muke24/Alert-Detector/Source/Images/background1.png

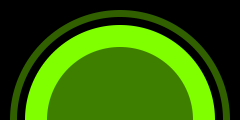
Source/Images/background1.png
