muke24/Alert-Detector/Source/Images/backgroundWhite1.png

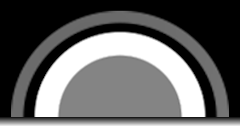
Source/Images/backgroundWhite1.png
