muke24/Alert-Detector/Source/Images/backgroundWhite.png

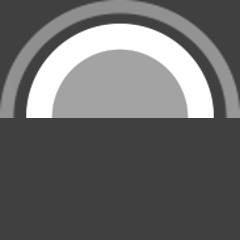
Source/Images/backgroundWhite.png
