muke24/Alert-Detector/Source/Images/In Use/Resources/Compass/compassBackground.png

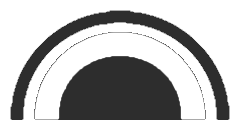
Source/Images/In Use/Resources/Compass/compassBackground.png
