muke24/Alert-Detector/Source/Images/In Use/Resources/Compass/compassBackground_1.png

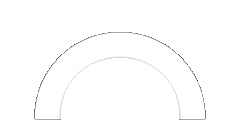
Source/Images/In Use/Resources/Compass/compassBackground_1.png
