muke24/Alert-Detector/Source/Images/In Use/Resources/Heat/heatBar1_full_img.png

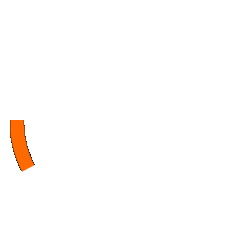
Source/Images/In Use/Resources/Heat/heatBar1_full_img.png
