muke24/Alert-Detector/Source/Images/In Use/Resources/Heat/heatBar2_full_img.png

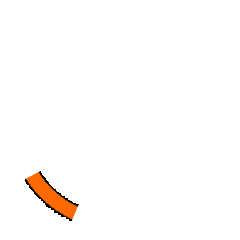
Source/Images/In Use/Resources/Heat/heatBar2_full_img.png
