muke24/Alert-Detector/Source/Images/In Use/Resources/Heat/heatBar3_full_img.png

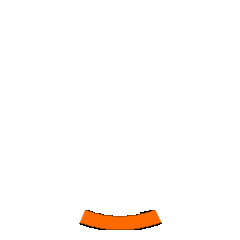
Source/Images/In Use/Resources/Heat/heatBar3_full_img.png
