muke24/Alert-Detector/Models/15/Print/Separate/ModuleHolder.stl

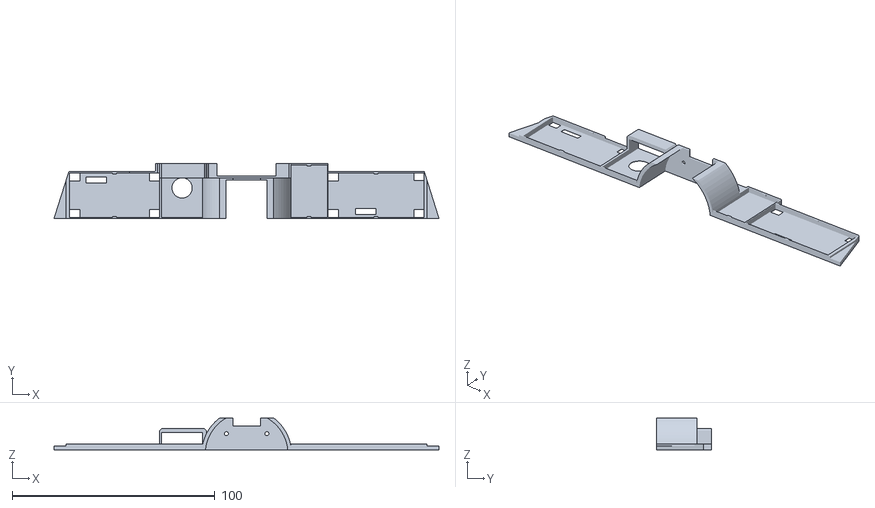
[picture p28: CAD file, 2025-08-17]
Models/15/Print/Separate/ModuleHolder.stl
189.9 x 27.0 x 15.7
