muke24/Alert-Detector/Models/New Small/Enclosure/01/Print/PoliceRadar03_Flipped.stl

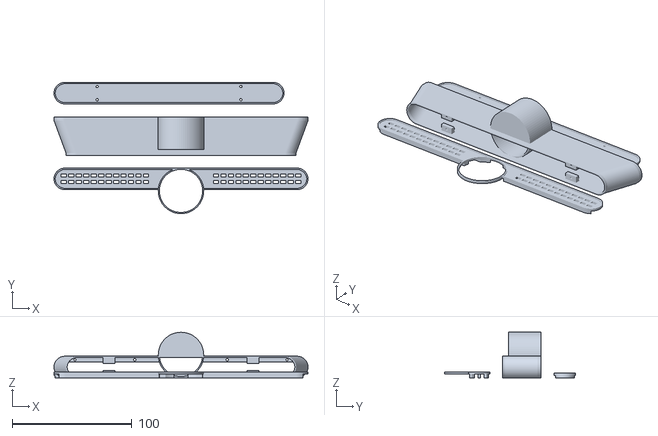
[picture p29: CAD file, 2025-07-22]
Models/New Small/Enclosure/01/Print/PoliceRadar03_Flipped.stl
212.0 x 109.6 x 38.0
