muke24/Alert-Detector/Models/New Small/Enclosure/01/Print/Separate/05/PoliceRadar05_Lid.stl

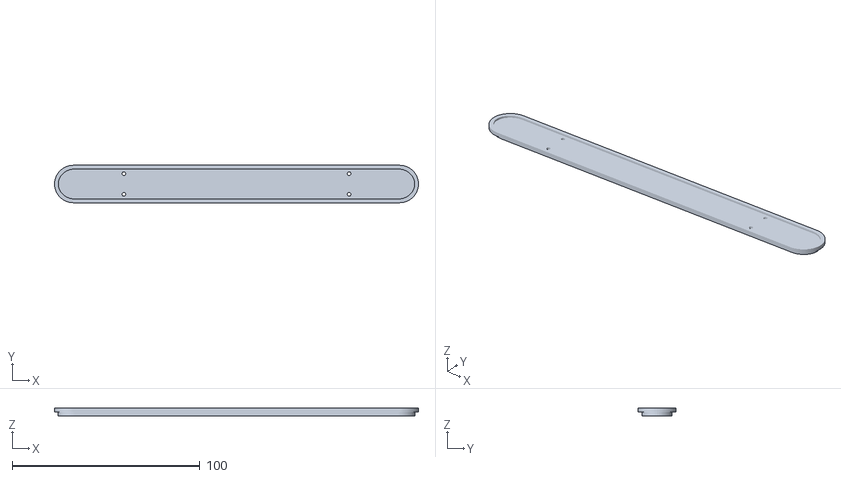
[picture p30: CAD file, 2025-07-22]
Models/New Small/Enclosure/01/Print/Separate/05/PoliceRadar05_Lid.stl
194.0 x 20.0 x 4.00
