muke24/Alert-Detector/Models/New Small/Enclosure/01/Print/Separate/07/PoliceRadar07_Enclosure.stl

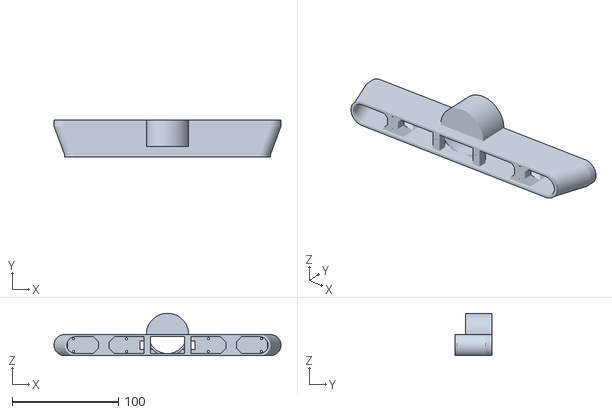
[picture p31: CAD file, 2025-07-23]
Models/New Small/Enclosure/01/Print/Separate/07/PoliceRadar07_Enclosure.stl
214.0 x 35.0 x 40.0
