muke24/Alert-Detector/Models/New Small/Enclosure/01/Print/Separate/Knob/03/Adapter.stl

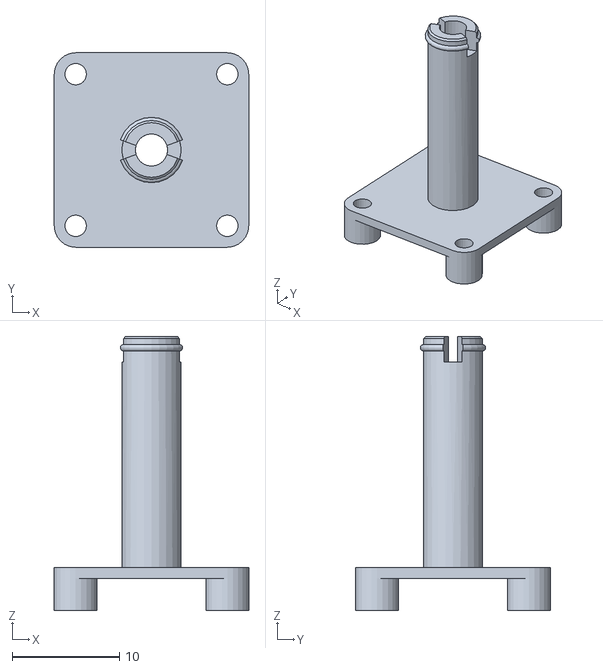
[picture p32: CAD file, 2025-07-28]
Models/New Small/Enclosure/01/Print/Separate/Knob/03/Adapter.stl
18.1 x 18.1 x 25.5
