muke24/Alert-Detector/Models/New Small/Enclosure/01/Print/Separate/Knob/Knobs02.stl

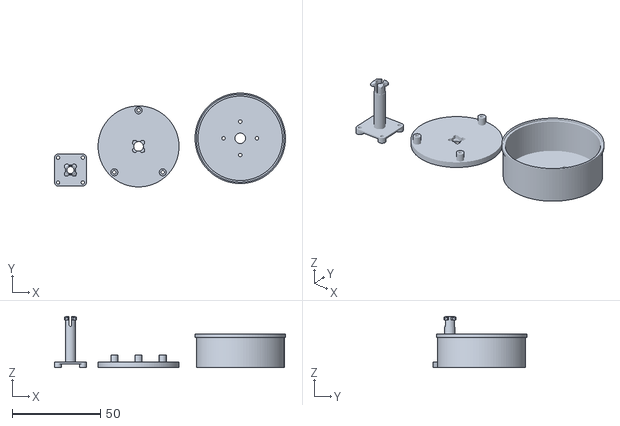
[picture p33: CAD file, 2025-07-28]
Models/New Small/Enclosure/01/Print/Separate/Knob/Knobs02.stl
131.2 x 53.3 x 29.0
