muke24/Alert-Detector/Models/New Small/iPower GM2804 Motor And Encoder Shell.stl

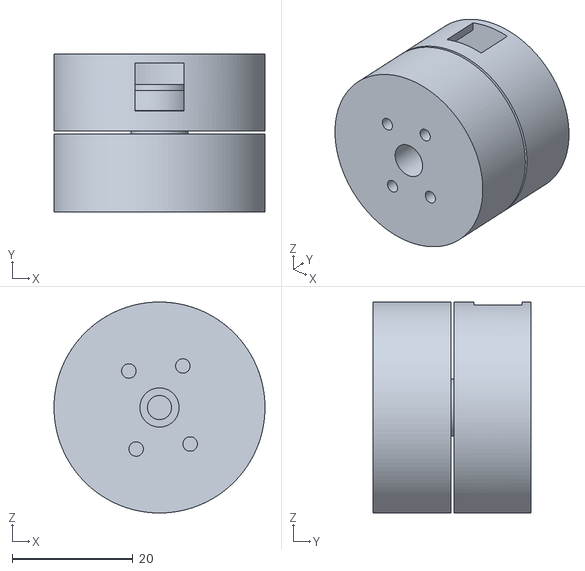
[picture p34: CAD file, 2025-07-22]
Models/New Small/iPower GM2804 Motor And Encoder Shell.stl
35.0 x 26.1 x 35.0
