muke24/Alert-Detector/Models/10/Print/Separate/Holder10.stl

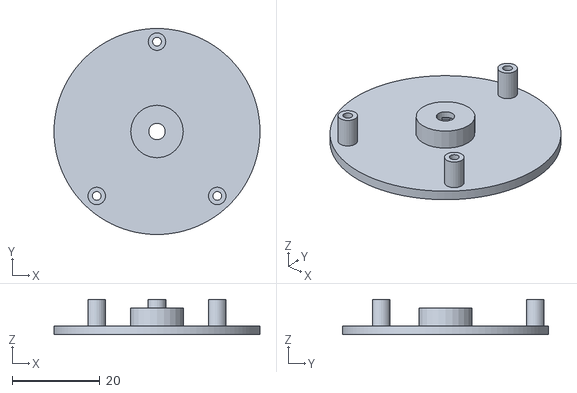
[picture p35: CAD file, 2025-07-29]
Models/10/Print/Separate/Holder10.stl
47.0 x 47.0 x 8.00
