muke24/Alert-Detector/Models/15/Print/Separate/AdapterHolder.stl

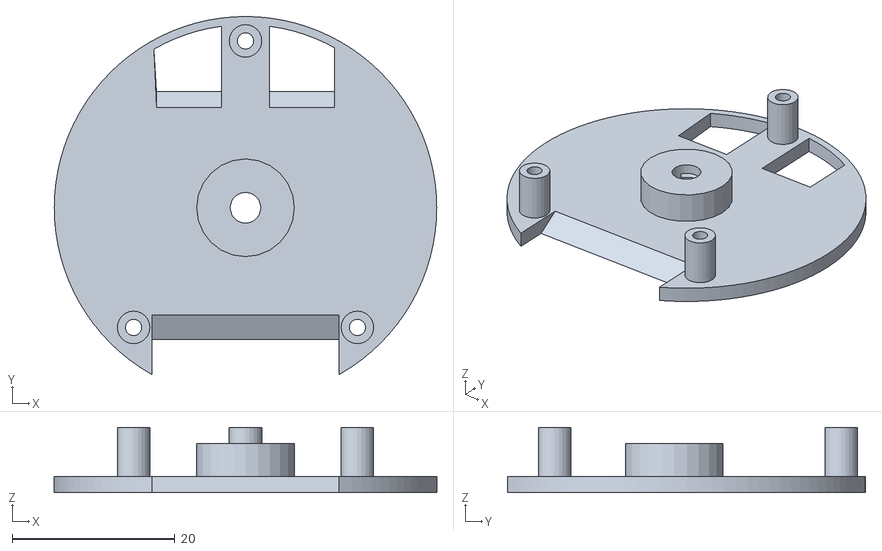
[picture p36: CAD file, 2025-08-17]
Models/15/Print/Separate/AdapterHolder.stl
47.0 x 44.0 x 8.00
