muke24/Alert-Detector/Models/New Small/Enclosure/01/Print/PoliceRadar05_Flipped.stl

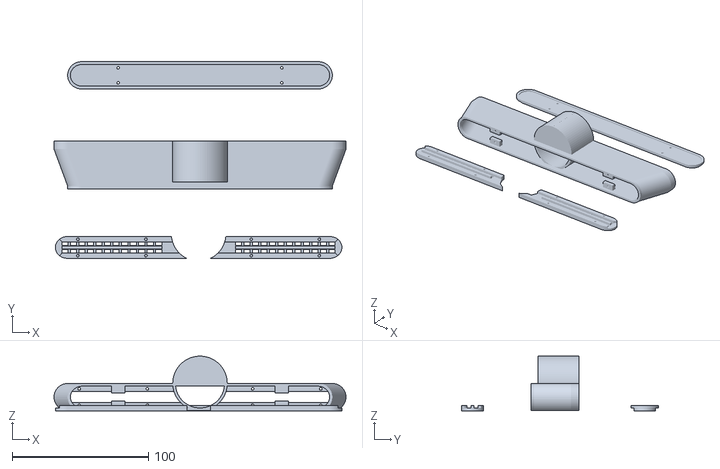
[picture p37: CAD file, 2025-07-22]
Models/New Small/Enclosure/01/Print/PoliceRadar05_Flipped.stl
214.0 x 144.2 x 40.1
