muke24/Alert-Detector/Models/New Small/Enclosure/01/Print/Separate/05/PoliceRadar05_Enclosure.stl

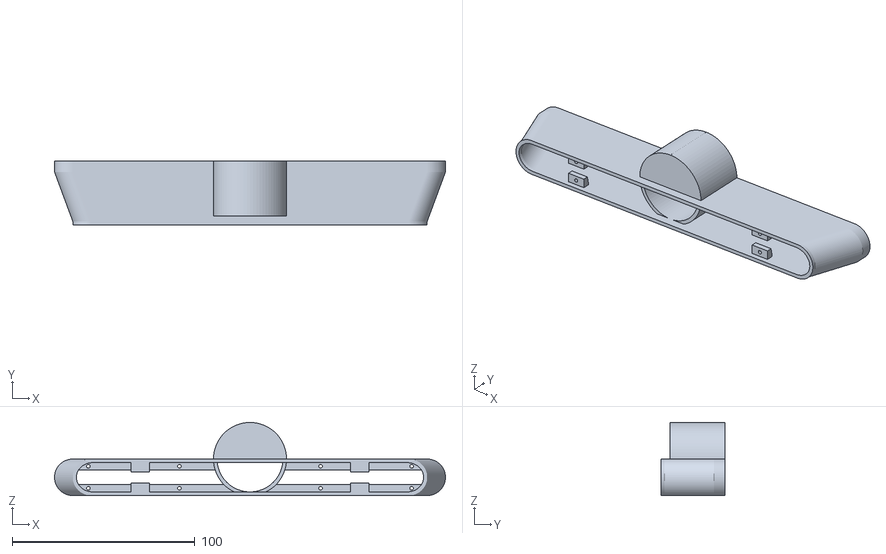
[picture p38: CAD file, 2025-07-22]
Models/New Small/Enclosure/01/Print/Separate/05/PoliceRadar05_Enclosure.stl
214.0 x 35.0 x 40.0
