muke24/Alert-Detector/Models/New Small/Enclosure/01/Print/Separate/06/PoliceRadar06_LedRack.stl

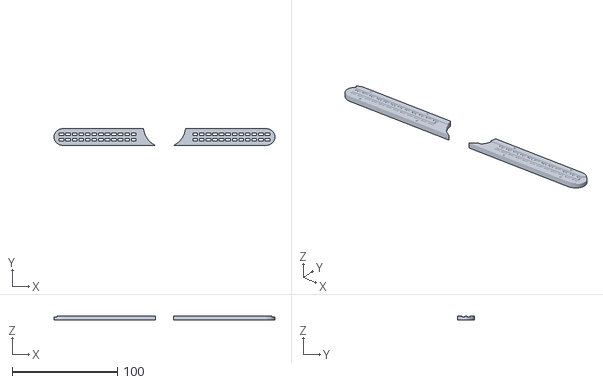
[picture p39: CAD file, 2025-07-22]
Models/New Small/Enclosure/01/Print/Separate/06/PoliceRadar06_LedRack.stl
210.0 x 16.0 x 4.00
