muke24/Alert-Detector/Models/New Small/Enclosure/01/Print/Separate/Knob/Knobs.stl

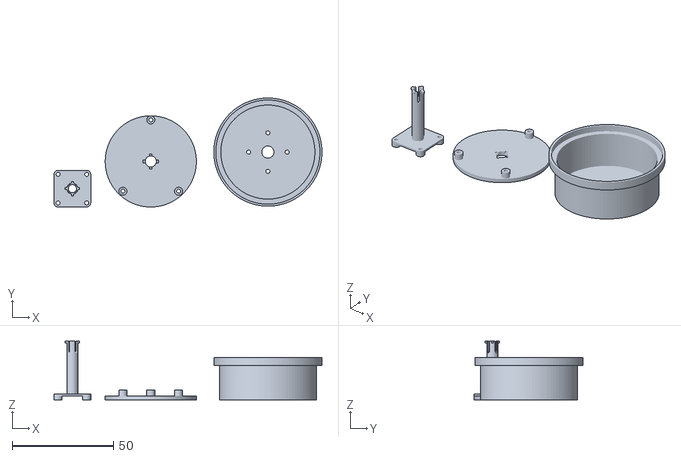
[picture p40: CAD file, 2025-07-26]
Models/New Small/Enclosure/01/Print/Separate/Knob/Knobs.stl
132.2 x 53.8 x 29.0
