muke24/Alert-Detector/Models/New Small/iPower GM2804 Encoder Shell.stl

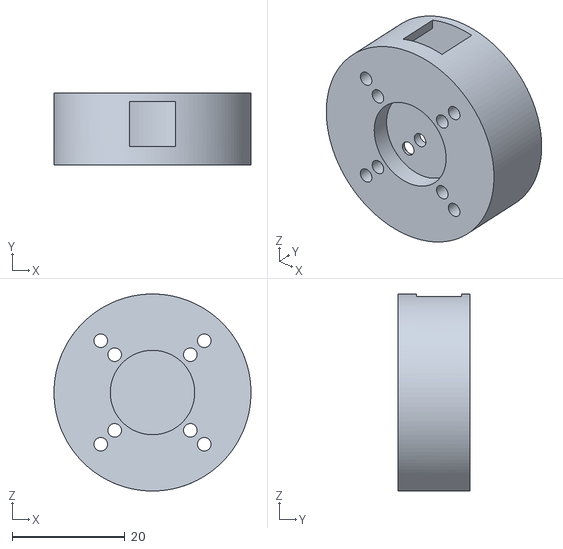
[picture p41: CAD file, 2025-07-22]
Models/New Small/iPower GM2804 Encoder Shell.stl
35.0 x 12.8 x 35.0
