muke24/Alert-Detector/Models/10/Print/Separate/Knob10.stl

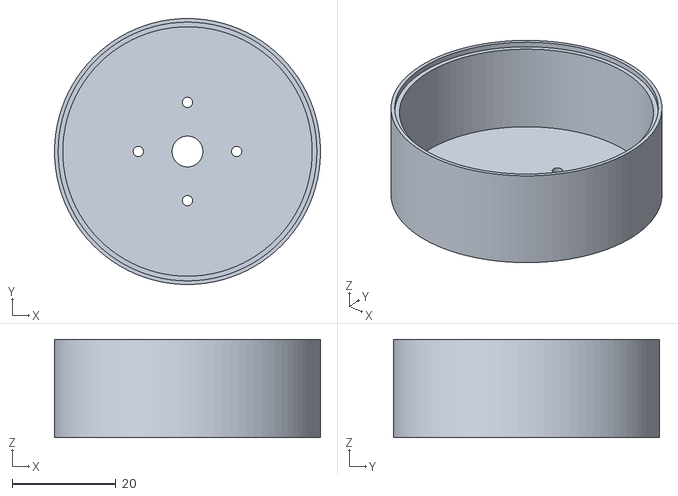
[picture p42: CAD file, 2025-07-29]
Models/10/Print/Separate/Knob10.stl
51.4 x 51.4 x 19.0
