muke24/Alert-Detector/Models/15/Print/Separate/LedRack.stl

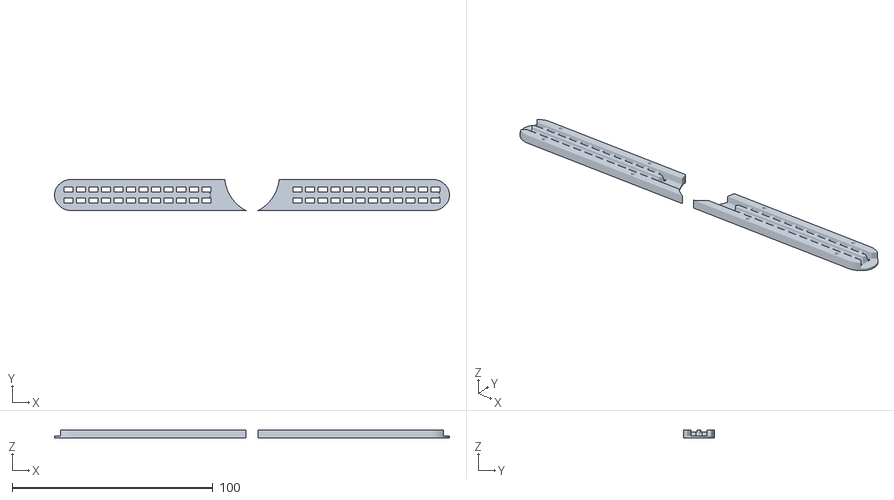
[picture p43: CAD file, 2025-08-17]
Models/15/Print/Separate/LedRack.stl
196.6 x 15.6 x 4.00
