muke24/Alert-Detector/Models/New Small/Enclosure/01/Print/Separate/Knob/01/ScreenHolder.stl

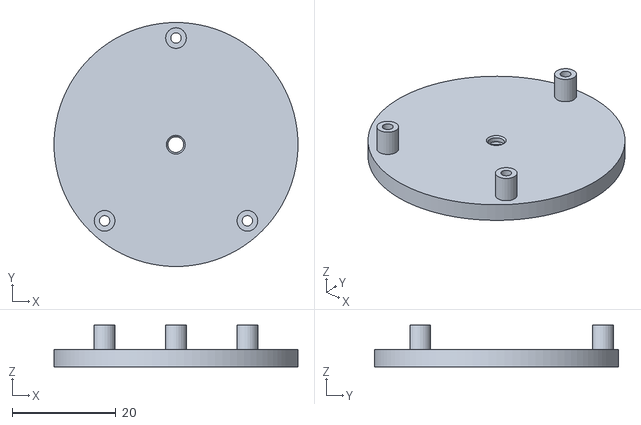
[picture p44: CAD file, 2025-07-28]
Models/New Small/Enclosure/01/Print/Separate/Knob/01/ScreenHolder.stl
47.0 x 47.0 x 8.00
