muke24/Alert-Detector/Models/13/Print/Separate/Holder.stl

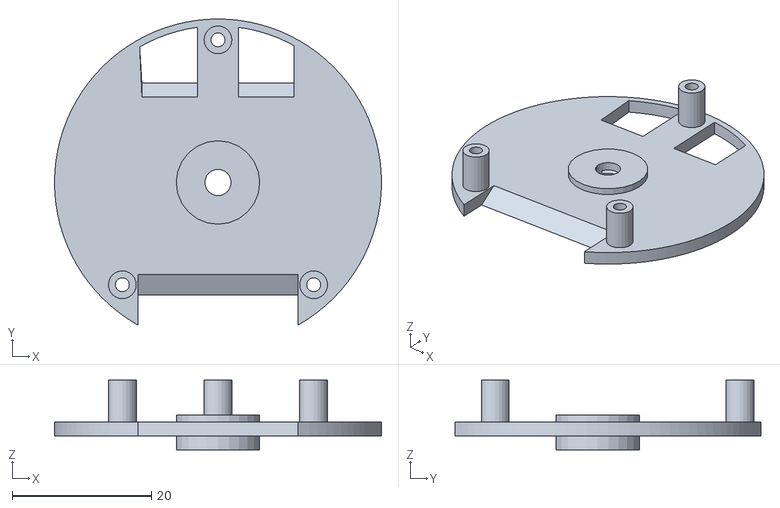
[picture p45: CAD file, 2025-08-06]
Models/13/Print/Separate/Holder.stl
47.0 x 44.0 x 10.0
