muke24/Alert-Detector/Models/14/Print/Separate/WiringHarness.stl

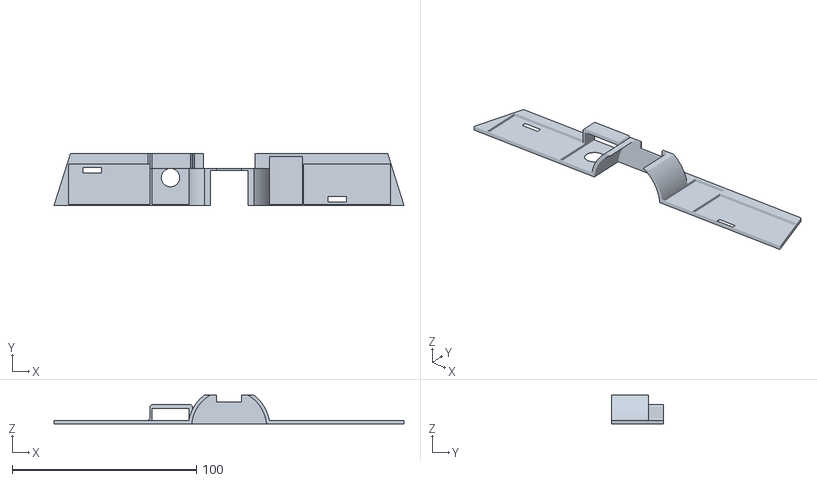
[picture p46: CAD file, 2025-08-13]
Models/14/Print/Separate/WiringHarness.stl
189.9 x 28.0 x 15.7
