muke24/Alert-Detector/Models/15/Print/Separate/Adapter.stl

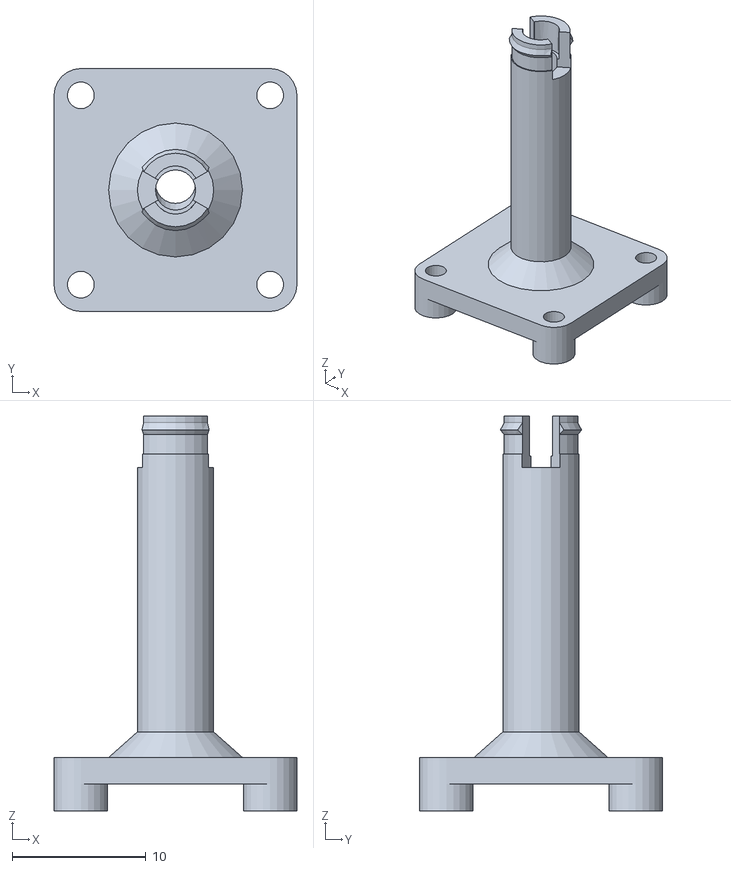
[picture p47: CAD file, 2025-08-17]
Models/15/Print/Separate/Adapter.stl
18.1 x 18.1 x 29.5
