muke24/Alert-Detector/Models/3D Prints/PoliceRadarPrototype_07_Lid.stl

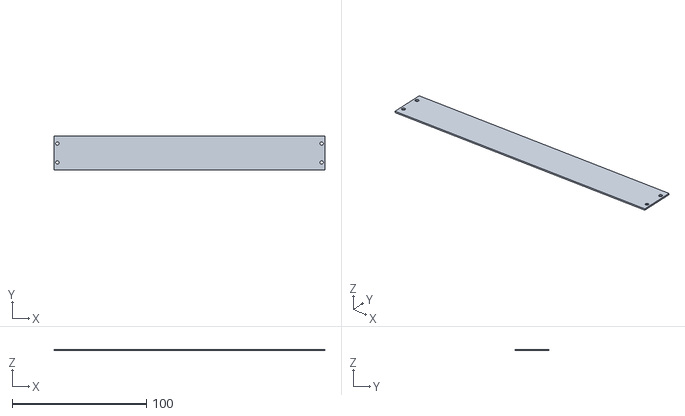
[picture p48: CAD file, 2025-05-03]
Models/3D Prints/PoliceRadarPrototype_07_Lid.stl
202.0 x 25.0 x 1.00
