muke24/Alert-Detector/Models/15/Print/Separate/Knob.stl

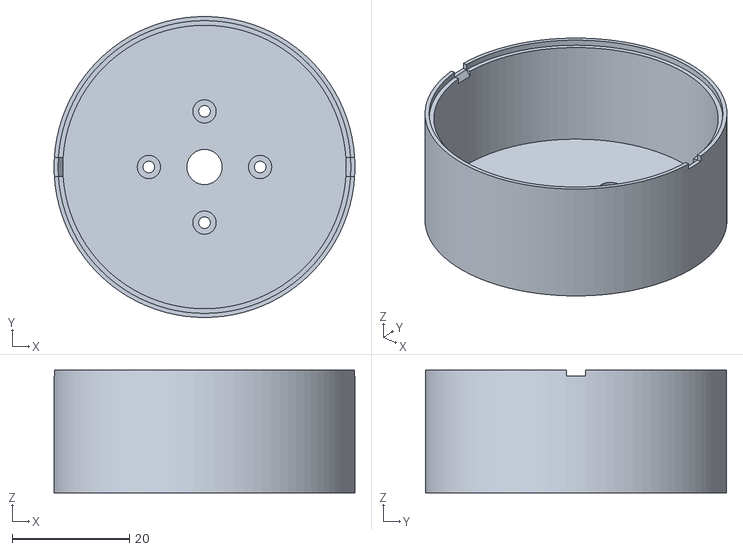
[picture p49: CAD file, 2025-08-17]
Models/15/Print/Separate/Knob.stl
51.4 x 51.4 x 21.0
