muke24/Alert-Detector/Models/New Small/Enclosure/01/Print/Separate/Knob/03/Holder07.stl

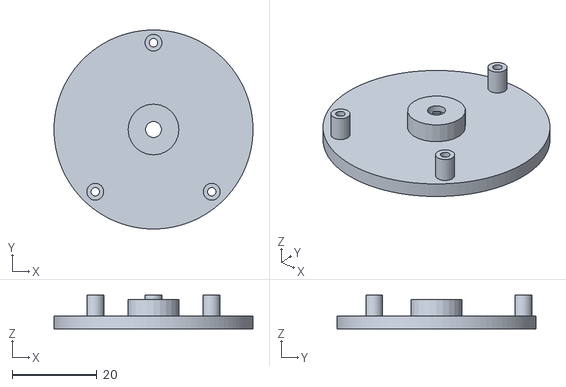
[picture p50: CAD file, 2025-07-28]
Models/New Small/Enclosure/01/Print/Separate/Knob/03/Holder07.stl
47.0 x 47.0 x 8.00
