muke24/Alert-Detector/Models/15/Print/Separate/Lid.stl

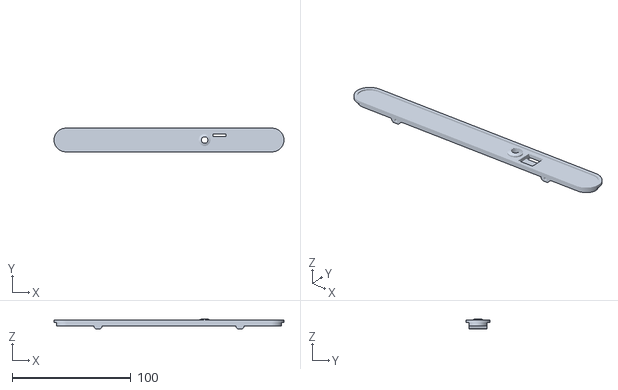
[picture p51: CAD file, 2025-08-17]
Models/15/Print/Separate/Lid.stl
194.0 x 20.0 x 8.40
