muke24/Alert-Detector/Models/15/Print/Separate/TransparentFrontPanel.stl

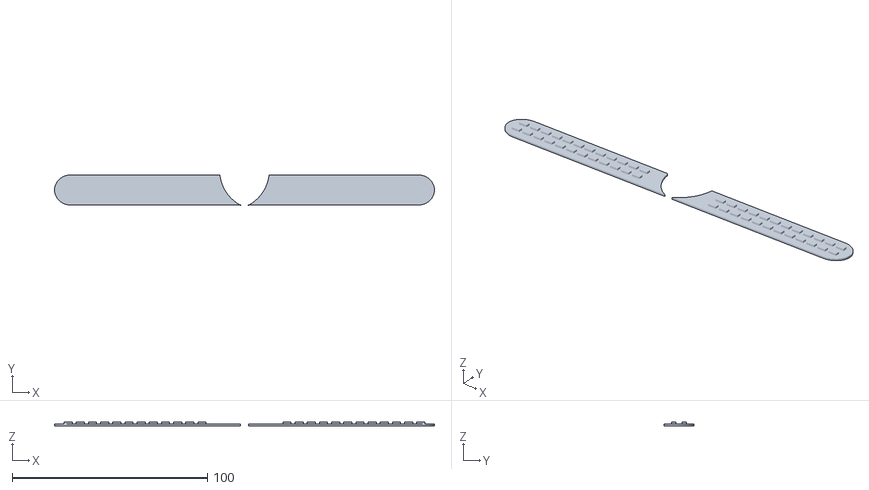
[picture p52: CAD file, 2025-08-17]
Models/15/Print/Separate/TransparentFrontPanel.stl
194.6 x 15.6 x 2.00
