muke24/Alert-Detector/Models/New Small/Enclosure/01/Print/Separate/Knob/03/Adapter07Holder.stl

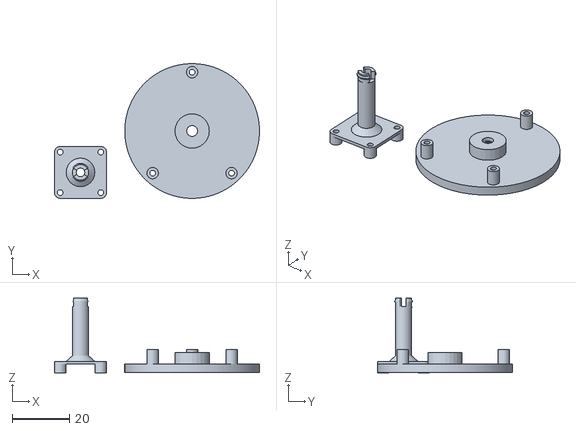
[picture p53: CAD file, 2025-07-28]
Models/New Small/Enclosure/01/Print/Separate/Knob/03/Adapter07Holder.stl
71.5 x 47.0 x 26.0
