muke24/Alert-Detector/Models/15/Print/Separate/WireHook.stl

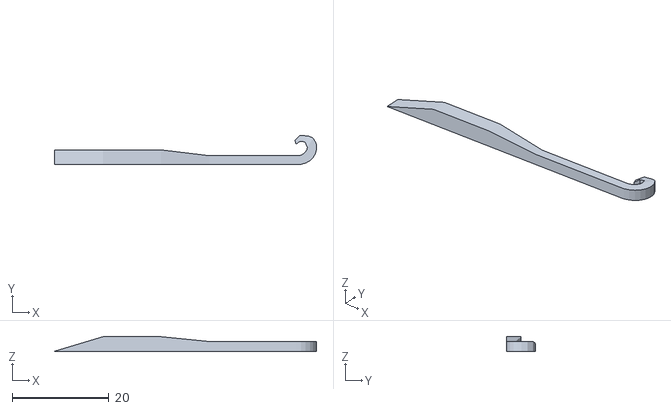
[picture p54: CAD file, 2025-08-17]
Models/15/Print/Separate/WireHook.stl
54.1 x 5.95 x 3.00
