muke24/Alert-Detector/Models/New Small/Enclosure/01/Print/Separate/Knob/03/Adapter01.stl

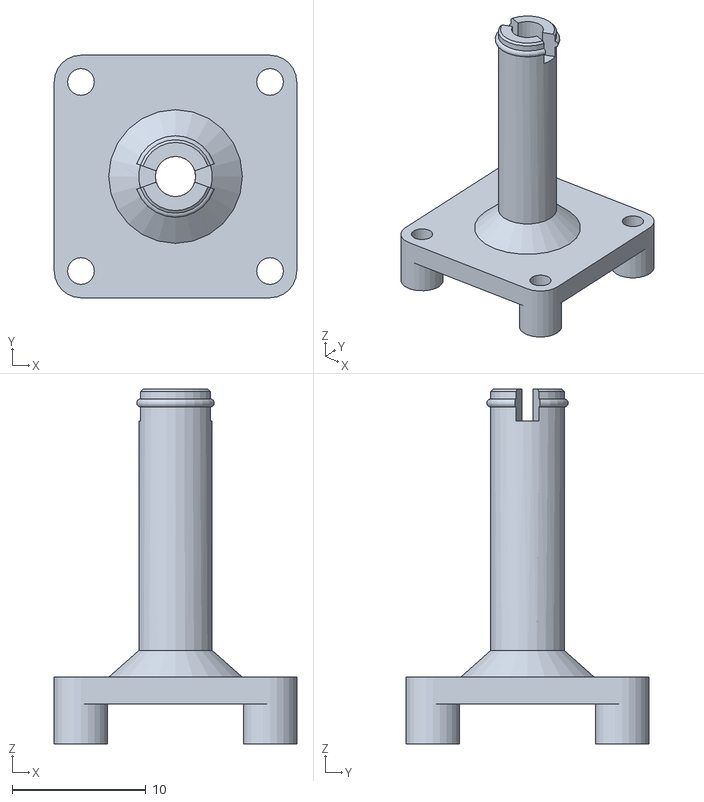
[picture p55: CAD file, 2025-07-28]
Models/New Small/Enclosure/01/Print/Separate/Knob/03/Adapter01.stl
18.1 x 18.1 x 26.5
