muke24/Alert-Detector/Models/15/Print/Separate/Enclosure.stl

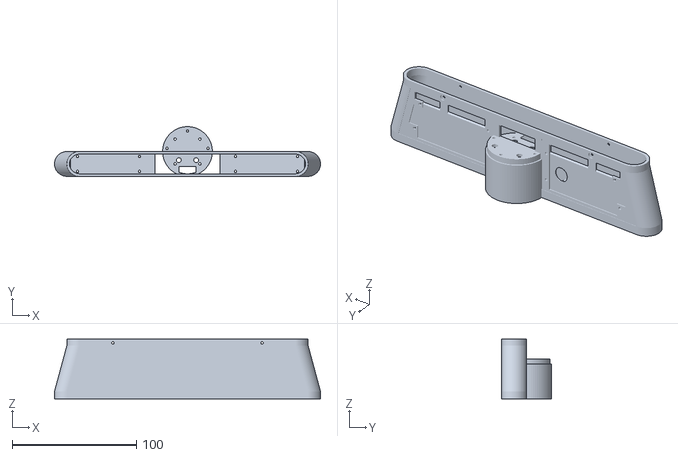
[picture p56: CAD file, 2025-08-17]
Models/15/Print/Separate/Enclosure.stl
214.0 x 40.0 x 48.0
