muke24/Alert-Detector/Models/15/Print/Separate/WireTrays.stl

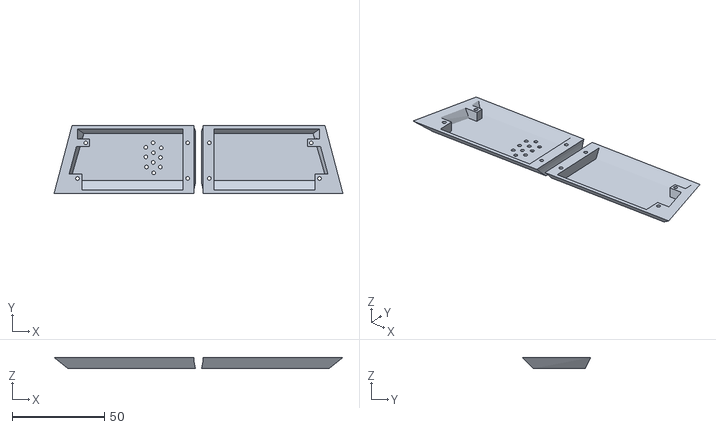
[picture p57: CAD file, 2025-08-17]
Models/15/Print/Separate/WireTrays.stl
156.6 x 37.0 x 6.00
