muke24/Alert-Detector/Assembly/Instructions/Instructions.png

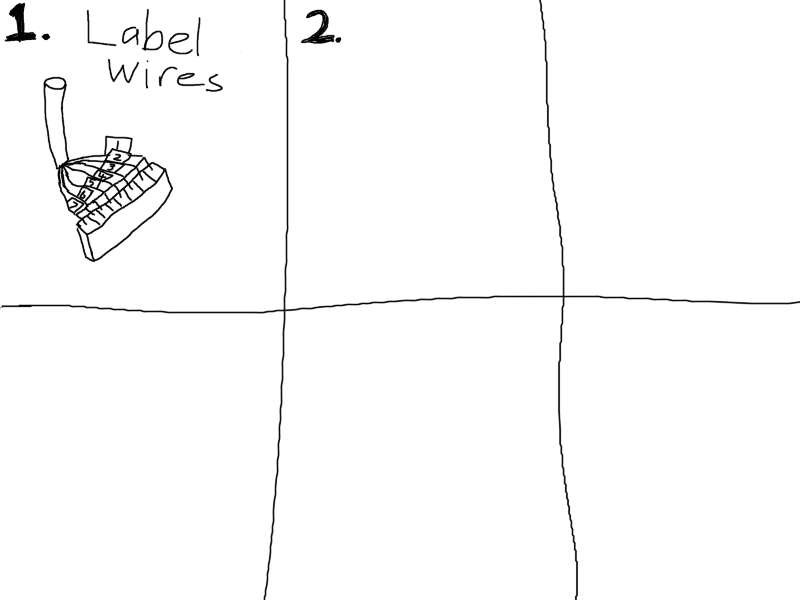
Assembly/Instructions/Instructions.png
