muke24/Alert-Detector/Project Documents/Wiring Diagrams/LED_Strips.png

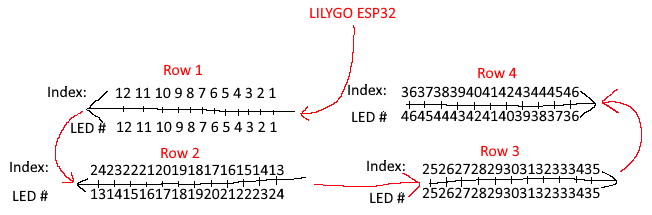
Project Documents/Wiring Diagrams/LED_Strips.png
