muke24/Alert-Detector/Code/Arduino/AlertRenderer/compassBackground.c

#ifdef __has_include
    #if __has_include("lvgl.h")
        #ifndef LV_LVGL_H_INCLUDE_SIMPLE
            #define LV_LVGL_H_INCLUDE_SIMPLE
        #endif
    #endif
#endif

#if defined(LV_LVGL_H_INCLUDE_SIMPLE)
    #include "lvgl.h"
#else
    #include "lvgl/lvgl.h"
#endif


#ifndef LV_ATTRIBUTE_MEM_ALIGN
#define LV_ATTRIBUTE_MEM_ALIGN
#endif

#ifndef LV_ATTRIBUTE_IMG_COMPASSBACKGROUND
#define LV_ATTRIBUTE_IMG_COMPASSBACKGROUND
#endif

const LV_ATTRIBUTE_MEM_ALIGN LV_ATTRIBUTE_LARGE_CONST LV_ATTRIBUTE_IMG_COMPASSBACKGROUND uint8_t compassBackground_map[] = {
  0x00, 0x00, 0x00, 0x00, 	/*Color of index 0*/
  0xff, 0xff, 0xff, 0xff, 	/*Color of index 1*/
  0x29, 0x29, 0x29, 0x1f, 	/*Color of index 2*/
  0xe3, 0xe3, 0xe3, 0xff, 	/*Color of index 3*/
  0x2d, 0x2d, 0x2d, 0x65, 	/*Color of index 4*/
  0xa6, 0xa6, 0xa6, 0xff, 	/*Color of index 5*/
  0x37, 0x37, 0x37, 0x7e, 	/*Color of index 6*/
  0x90, 0x90, 0x90, 0xff, 	/*Color of index 7*/
  0x33, 0x33, 0x33, 0x97, 	/*Color of index 8*/
  0x81, 0x81, 0x81, 0xff, 	/*Color of index 9*/
  0x6c, 0x6c, 0x6c, 0xff, 	/*Color of index 10*/
  0x5b, 0x5b, 0x5b, 0xff, 	/*Color of index 11*/
  0x4f, 0x4f, 0x4f, 0xff, 	/*Color of index 12*/
  0x3b, 0x3b, 0x3b, 0xff, 	/*Color of index 13*/
  0x32, 0x32, 0x32, 0xff, 	/*Color of index 14*/
  0x2d, 0x2d, 0x2d, 0xff, 	/*Color of index 15*/

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
};

const lv_img_dsc_t compassBackground = {
  .header.cf = LV_IMG_CF_INDEXED_4BIT,
  .header.always_zero = 0,
  .header.reserved = 0,
  .header.w = 240,
  .header.h = 120,
  .data_size = 14464,
  .data = compassBackground_map,
};
