muke24/Alert-Detector/Code/1_75 Inch/AlertFinder/Compass.cpp

/**
 * @file      Compass.cpp
 * @author    Peter Thompson
 * @brief     Implementation of the Compass module, now using LIS3MDL Magnetometer.
 * @version   2.03 (Corrected Axis Remapping)
 * @date      2025-07-31
 *
 * @copyright Copyright (c) 2025
 *
 */

#include "Compass.h"
#include <Wire.h>
#include "SensorQMI8658.hpp"
// Using the Adafruit LIS3MDL library for the new magnetometer.
#include <Adafruit_LIS3MDL.h>
#include <Adafruit_Sensor.h>
#include "MadgwickAHRS.h"
#include "HWCDC.h" // For USBSerial printing

// --- Sensor Objects ---
static SensorQMI8658 qmi;
// Instantiate the LIS3MDL sensor object.
static Adafruit_LIS3MDL mag;
static Madgwick filter;

// --- Module State ---
static bool qmi_ready = false;
static bool mag_ready = false;
static float heading = 0.0f;
static int orientation = 0; // 0 = normal, 1 = flipped

// Magnetic declination for Springfield, NSW, Australia (approximate)
const float MAGNETIC_DECLINATION = 12.5;

/**
 * @brief Initializes the sensors on the main I2C bus.
 */
bool compass_setup() {
    // The QMI8658 is on the main I2C bus (Wire)
    if (qmi.begin(Wire, QMI8658_L_SLAVE_ADDRESS)) {
        qmi.configAccelerometer(SensorQMI8658::ACC_RANGE_4G, SensorQMI8658::ACC_ODR_1000Hz, SensorQMI8658::LPF_MODE_3);
        qmi.configGyroscope(SensorQMI8658::GYR_RANGE_512DPS, (SensorQMI8658::GyroODR)SensorQMI8658::ACC_ODR_1000Hz, SensorQMI8658::LPF_MODE_3);
        qmi_ready = true;
        USBSerial.println("Compass module setup: QMI8658 IMU FOUND.");
    } else {
        USBSerial.println("Compass module setup: QMI8658 IMU NOT FOUND.");
    }

    // Initialize the LIS3MDL magnetometer.
    // The begin_I2C() function returns true if the sensor is found and initialized.
    if (mag.begin_I2C()) {
        // Configure the LIS3MDL for best performance and to avoid saturation.
        // Set range to a high value to prevent magnetic saturation.
        mag.setRange(LIS3MDL_RANGE_16_GAUSS);
        // Set performance mode and data rate to match the IMU and filter.
        mag.setPerformanceMode(LIS3MDL_ULTRAHIGHMODE);
        mag.setDataRate(LIS3MDL_DATARATE_1000_HZ);
        
        mag_ready = true;
        USBSerial.println("Compass module setup: LIS3MDL FOUND.");
    } else {
        mag_ready = false;
        USBSerial.println("Compass module setup: LIS3MDL NOT FOUND.");
    }

    // Match the filter's sample rate to the sensor's ODR (1000Hz)
    filter.begin(1000); 

    return qmi_ready && mag_ready;
}
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
